jhud/hackwatch/states.h

// (c)2018 James Hudson, released under the MIT license

#ifndef STATES_H
#define STATES_H

enum State {
	StateTime,
  StateMenu,
  StateStopwatch,
  StateTimer,
	StateFlashlight,
  StateEnvironment,
  StateWifiScan
};

#endif
