jhud/hackwatch/SSD1331Extended.h

/**
 * The MIT License (MIT)
 *
 * Copyright (c) 2016 by Daniel Eichhorn
 * Copyright (c) 2016 by Fabrice Weinberg
 * Modified Work Copyright (c) 2018 by James Hudson
 *
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
 * Credits for parts of this code go to Mike Rankin. Thank you so much for sharing!
 */

#ifndef OLEDDISPLAY_h
#define OLEDDISPLAY_h

#include <Arduino.h>
#include "ESP32_SSD1331.h"


//#define DEBUG_OLEDDISPLAY(...) Serial.printf( __VA_ARGS__ )

#ifndef DEBUG_OLEDDISPLAY
#define DEBUG_OLEDDISPLAY(...)
#endif


// Display settings
#define DISPLAY_WIDTH 96
#define DISPLAY_HEIGHT 64

// Header Values
#define JUMPTABLE_BYTES 4

#define JUMPTABLE_LSB   1
#define JUMPTABLE_SIZE  2
#define JUMPTABLE_WIDTH 3
#define JUMPTABLE_START 4

#define WIDTH_POS 0
#define HEIGHT_POS 1
#define FIRST_CHAR_POS 2
#define CHAR_NUM_POS 3



#ifndef _swap_int16_t
#define _swap_int16_t(a, b) { int16_t t = a; a = b; b = t; }
#endif

#define RGB16(r, g, b) ((b << 11) | (r << 5) | (g))
#define C_R(color) ((color>>5)&31)
#define C_G(color) ((color)&63)
#define C_B(color) ((color>>11))

// Note that green has an extra bit
enum OLEDDISPLAY_COLOR {
  BLACK = 0,
  WHITE = 0xFFFF,
  DARK_GRAY = RGB16(1,2,1),
  GRAY = RGB16(2,4,2),
  LIGHT_BLUE = RGB16(2,3,31),
  BLUE = RGB16(0, 0, 31),
  RED = RGB16(20,0, 0), // Red does not like to go above 20 for some reason
  GREEN = RGB16(0,63,0),
  YELLOW = RGB16(31,63,0),
  ORANGE = RGB16(31,31,0),
  VIOLET = RGB16(20,0, 31),
  MAGENTA = RGB16(31,0, 31),
  
  INVERSE = 2
};

enum OLEDDISPLAY_TEXT_ALIGNMENT {
  TEXT_ALIGN_LEFT = 0,
  TEXT_ALIGN_RIGHT = 1,
  TEXT_ALIGN_CENTER = 2,
  TEXT_ALIGN_CENTER_BOTH = 3
};


class SSD1331Extended : public ESP32_SSD1331 {
  public:
	  SSD1331Extended(uint8_t sck, uint8_t miso, uint8_t mosi, uint8_t cs, uint8_t dc, uint8_t rst); 

    // Draws a string at the given location
    void drawString(int16_t x, int16_t y, String text, uint16_t color);

    // Draws a String with a maximum width at the given location.
    // If the given String is wider than the specified width
    // The text will be wrapped to the next line at a space or dash
    void drawStringMaxWidth(int16_t x, int16_t y, uint16_t maxLineWidth, String text, uint16_t color);

    // Returns the width of the const char* with the current
    // font settings
    uint16_t getStringWidth(const char* text, uint16_t length);

    // Convencience method for the const char version
    uint16_t getStringWidth(String text);

    // Specifies relative to which anchor point
    // the text is rendered. Available constants:
    // TEXT_ALIGN_LEFT, TEXT_ALIGN_CENTER, TEXT_ALIGN_RIGHT, TEXT_ALIGN_CENTER_BOTH
    void setTextAlignment(OLEDDISPLAY_TEXT_ALIGNMENT textAlignment);

    // Sets the current font. Available default fonts
    // ArialMT_Plain_10, ArialMT_Plain_16, ArialMT_Plain_24
    void setFont(const char *fontData);

    /* Display functions */

  void drawInternal(int16_t xMove, int16_t yMove, int16_t width, int16_t height, const char *data, uint16_t offset, uint16_t bytesInData,  uint16_t color); //__attribute__((always_inline));


  protected:

    OLEDDISPLAY_TEXT_ALIGNMENT   textAlignment = TEXT_ALIGN_LEFT;
    uint16_t            color         = WHITE;

    const char          *fontData              = 0;

    // converts utf8 characters to extended ascii
    static char* utf8ascii(String s);
    static byte utf8ascii(byte ascii);

    void drawStringInternal(int16_t xMove, int16_t yMove, char* text, uint16_t textLength, uint16_t textWidth, uint16_t color);

};

#endif
